jmos1/28PINS_V01/3D Models/c0805_1.25mm_height.STEP

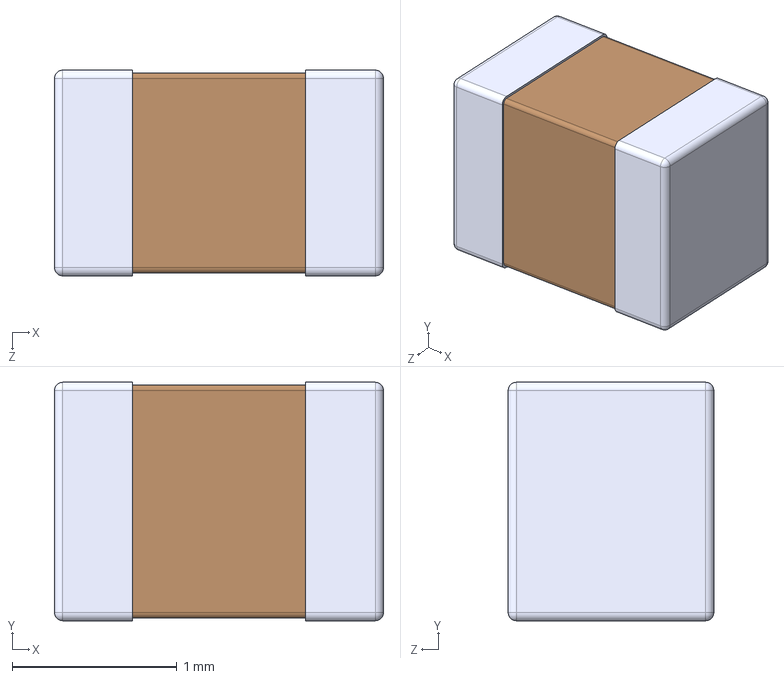
[picture p18: CAD file, 2020-04-26]
3D Models/c0805_1.25mm_height.STEP
2.00 x 1.45 x 1.25 mm
