jmos1/28PINS_V01/3D Models/ABM7.STEP

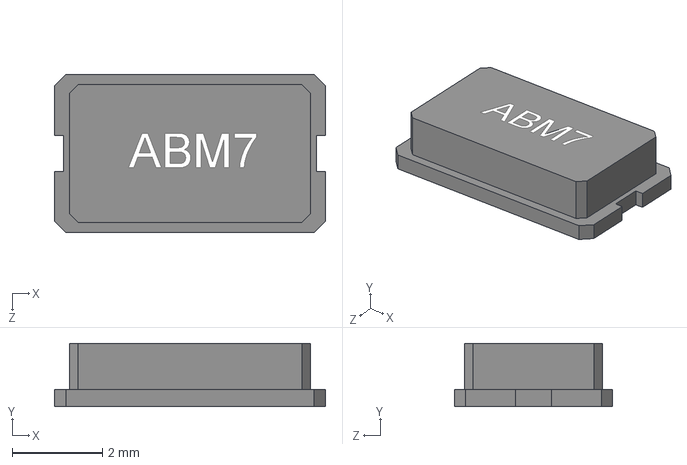
[picture p19: CAD file, 2020-04-26]
3D Models/ABM7.STEP
5.99 x 1.40 x 3.51 mm
