jmos1/28PINS_V01/3D Models/sw_1825910-6.step

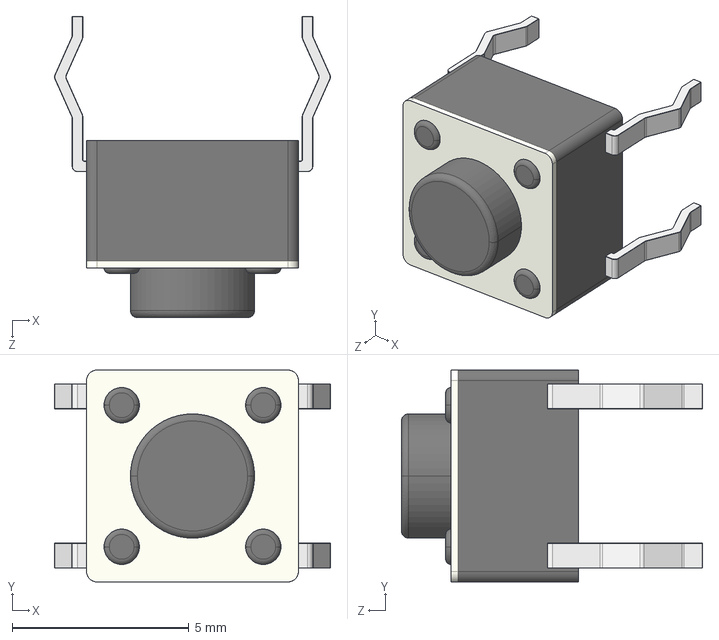
[picture p20: CAD file, 2020-04-26]
3D Models/sw_1825910-6.step
7.80 x 5.99 x 8.51 mm
