jmos1/28PINS_V01/3D Models/dip_28.step

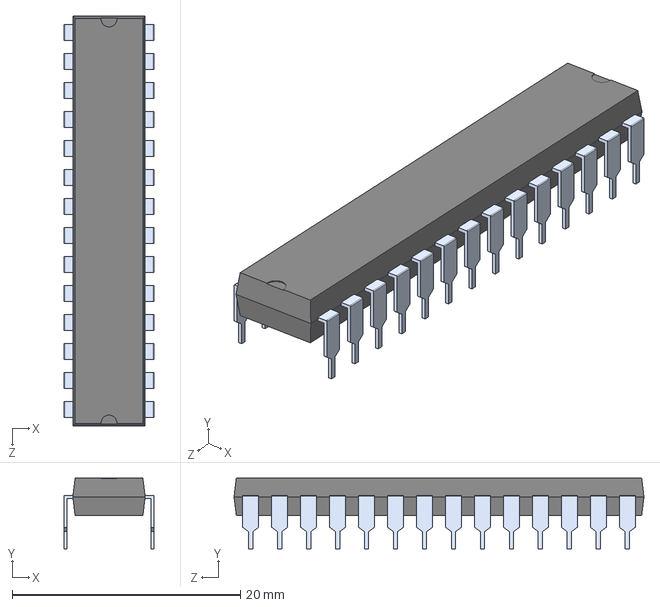
[picture p21: CAD file, 2020-04-26]
3D Models/dip_28.step
7.87 x 6.22 x 35.9 mm
