jmos1/28PINS_V01/3D Models/usb_micro_female.STEP

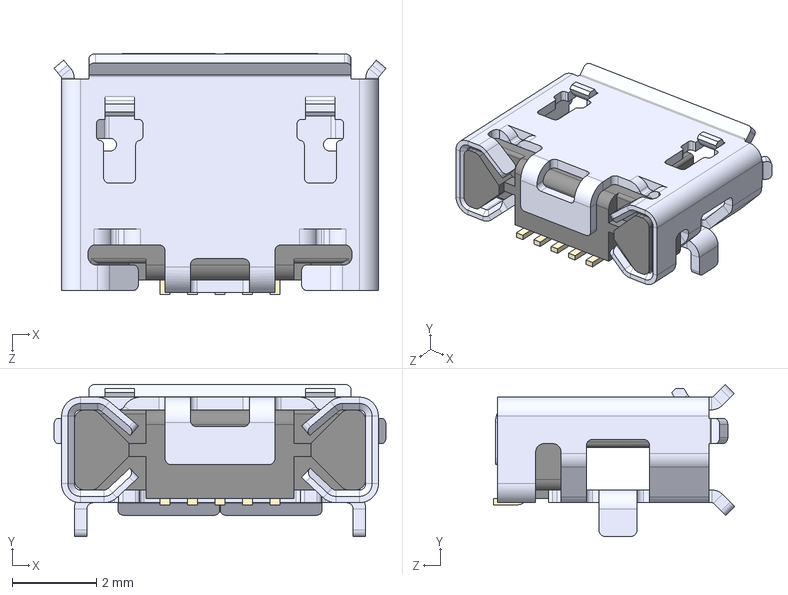
[picture p22: CAD file, 2020-04-26]
3D Models/usb_micro_female.STEP
7.86 x 3.60 x 5.71 mm
