jmos1/28PINS_V01/3D Models/r0805.STEP

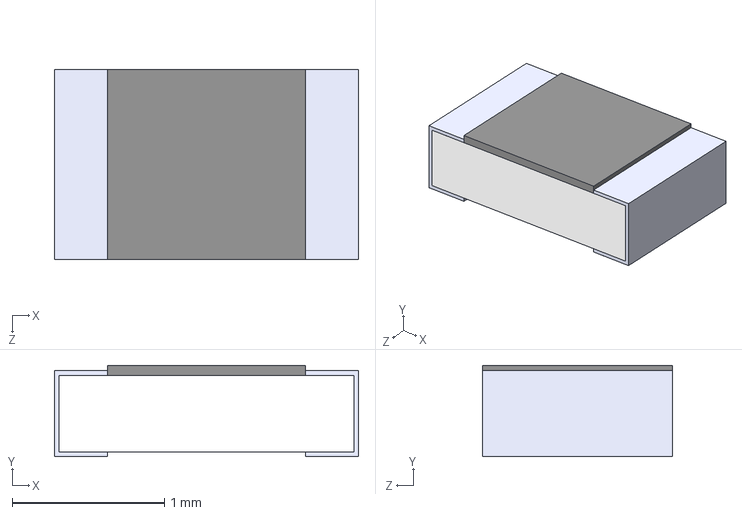
[picture p23: CAD file, 2020-04-26]
3D Models/r0805.STEP
2.00 x 0.6 x 1.25 mm
