jmos1/28PINS_V01/3D Models/hdr_female_1x8_2.54.stp

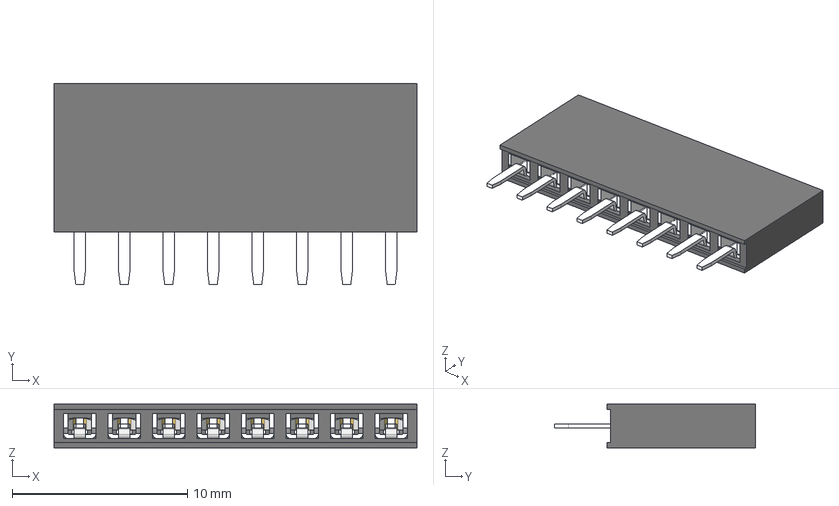
[picture p24: CAD file, 2020-04-26]
3D Models/hdr_female_1x8_2.54.stp
20.7 x 11.5 x 2.50 mm
M20-78208_MOULD
M20-782_CONTACT x 8
